wangdongxuking61/2015-Electronical-Competition-Code---Renesas-Cup/pictures/CAM00122.jpg

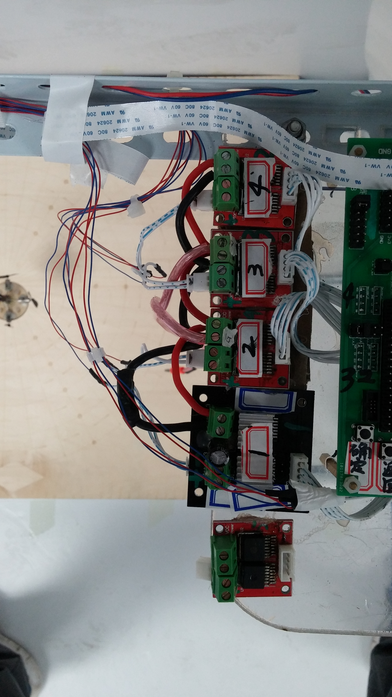
pictures/CAM00122.jpg
