wangdongxuking61/2015-Electronical-Competition-Code---Renesas-Cup/pictures/CAM00124.jpg

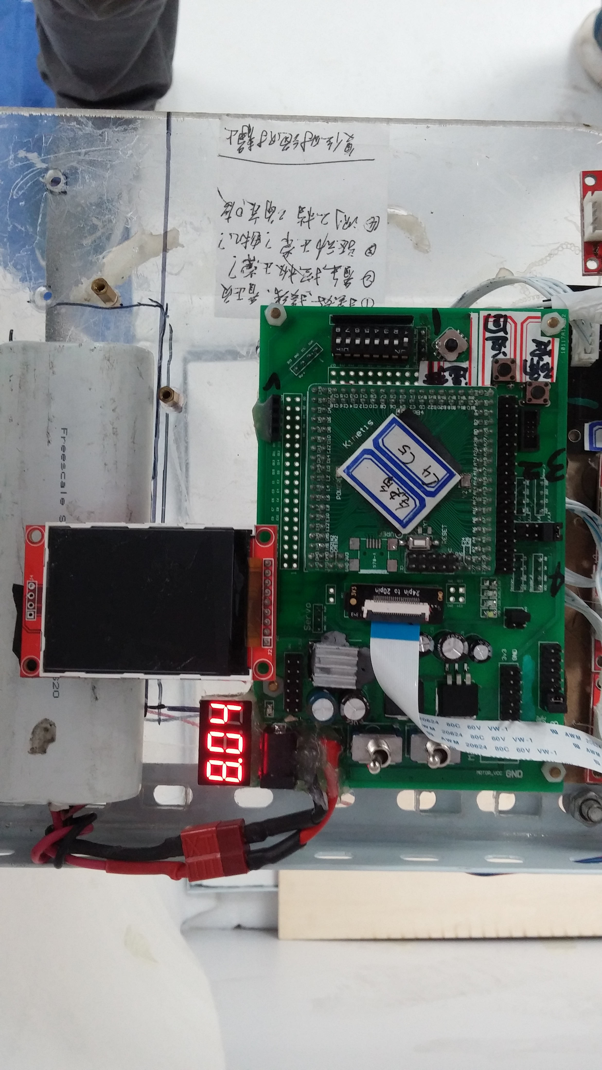
pictures/CAM00124.jpg
