wangdongxuking61/2015-Electronical-Competition-Code---Renesas-Cup/pictures/CAM00125.jpg

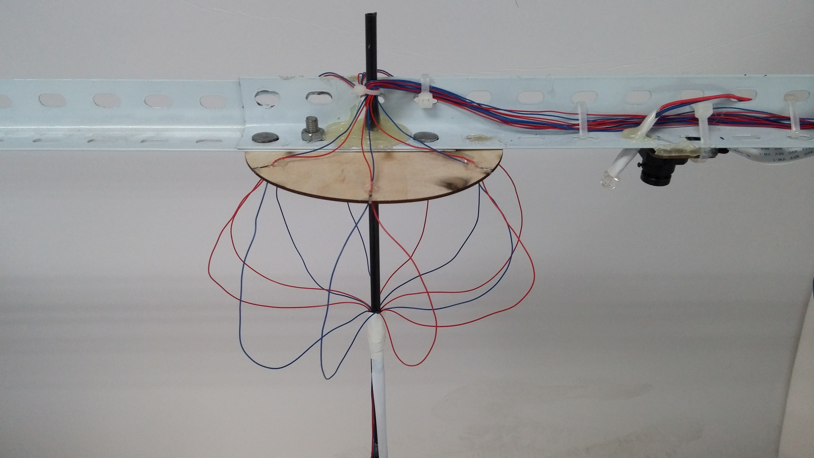
pictures/CAM00125.jpg
