wangdongxuking61/2015-Electronical-Competition-Code---Renesas-Cup/pictures/CAM00126.jpg

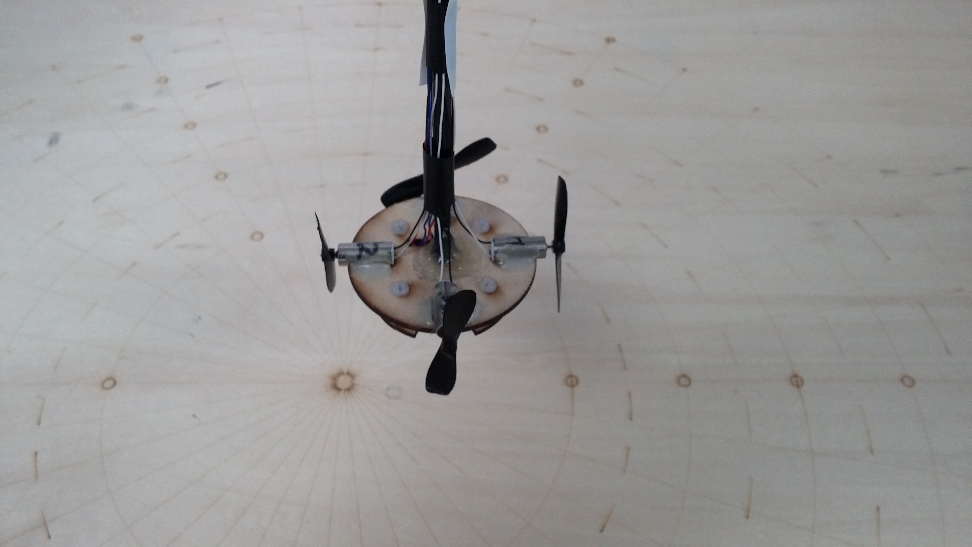
pictures/CAM00126.jpg
