wangdongxuking61/2015-Electronical-Competition-Code---Renesas-Cup/pictures/CAM00128.jpg

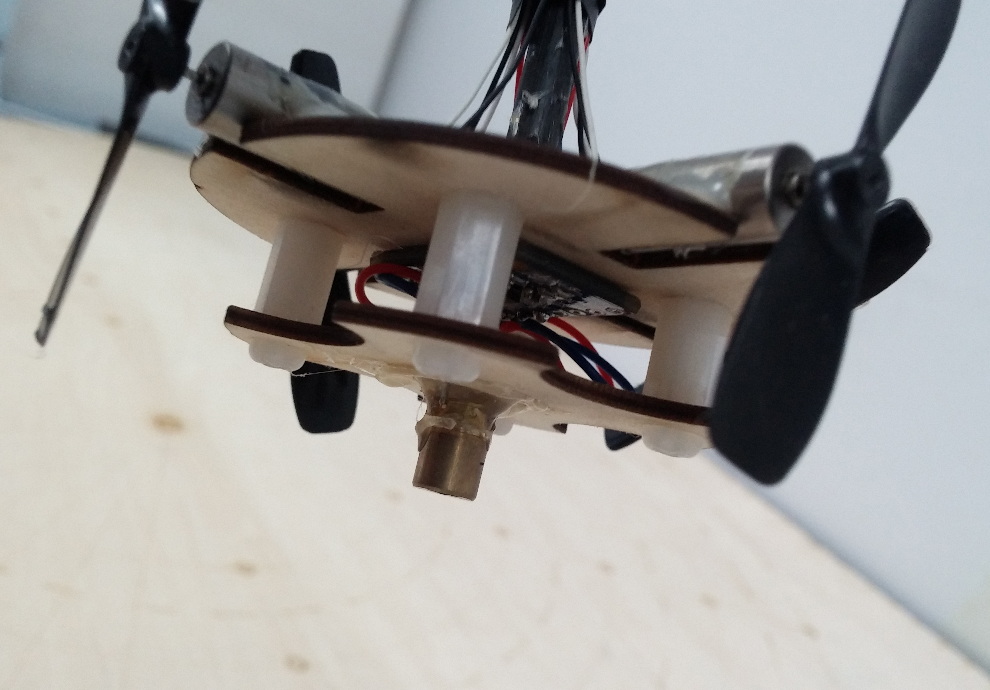
pictures/CAM00128.jpg
