wangdongxuking61/2015-Electronical-Competition-Code---Renesas-Cup/pictures/CAM00131.jpg

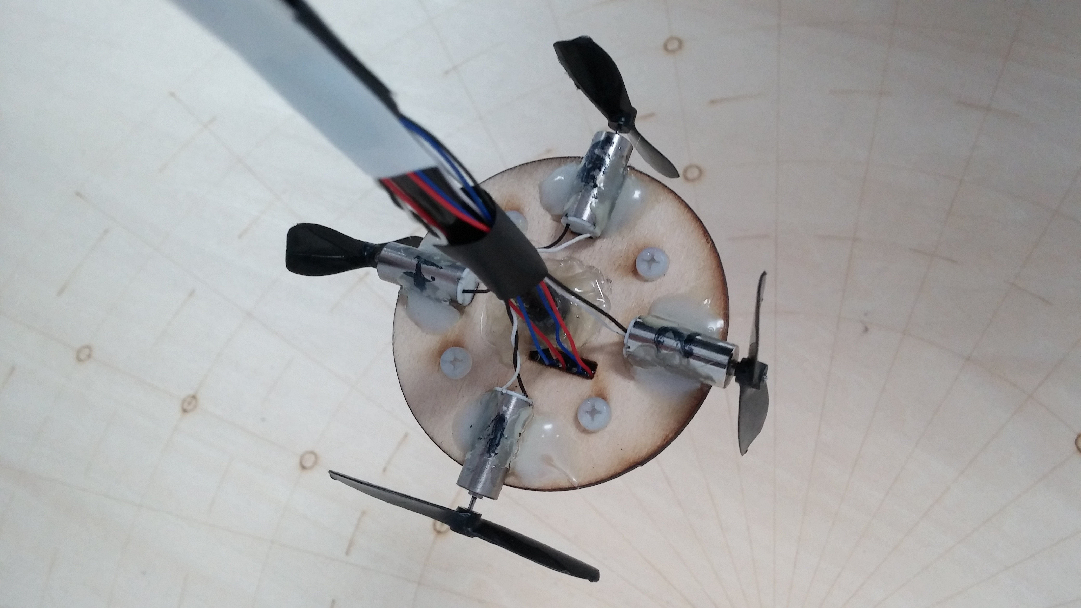
pictures/CAM00131.jpg
