wangdongxuking61/2015-Electronical-Competition-Code---Renesas-Cup/pictures/CAM00132.jpg

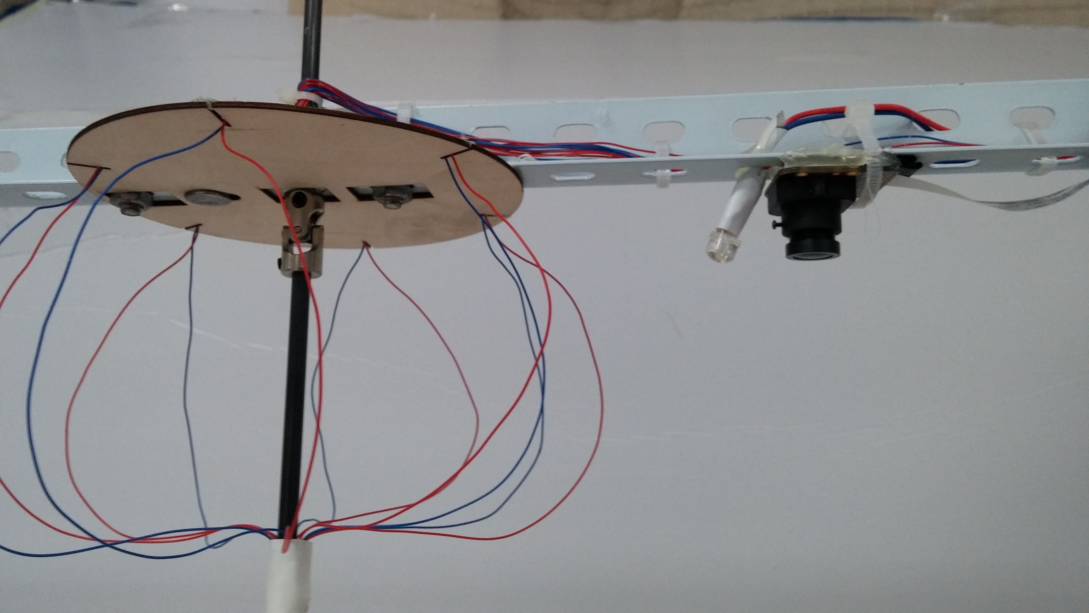
pictures/CAM00132.jpg
