wangdongxuking61/2015-Electronical-Competition-Code---Renesas-Cup/pictures/QQ截图20151103121053.png

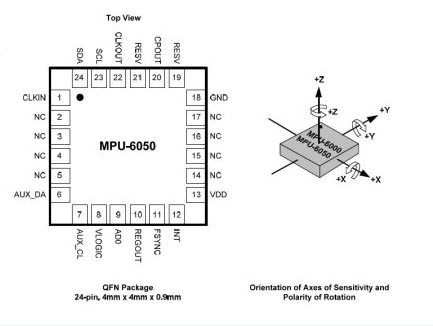
pictures/QQ截图20151103121053.png
