wangdongxuking61/2015-Electronical-Competition-Code---Renesas-Cup/pictures/TB1RlANHXXXXXb.XFXXXXXXXXXX_!!0-item_pic.jpg_400x400.jpg

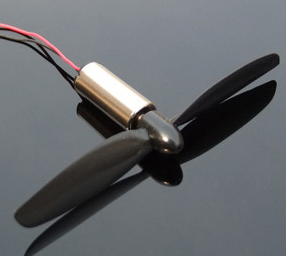
pictures/TB1RlANHXXXXXb.XFXXXXXXXXXX_!!0-item_pic.jpg_400x400.jpg
