wangdongxuking61/2015-Electronical-Competition-Code---Renesas-Cup/pictures/底座_下.png

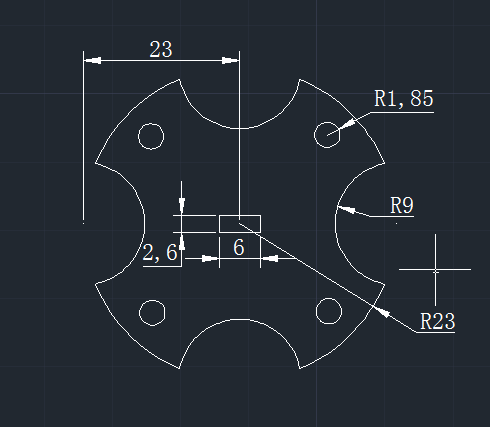
pictures/底座_下.png
