wangdongxuking61/2015-Electronical-Competition-Code---Renesas-Cup/pictures/电源.png

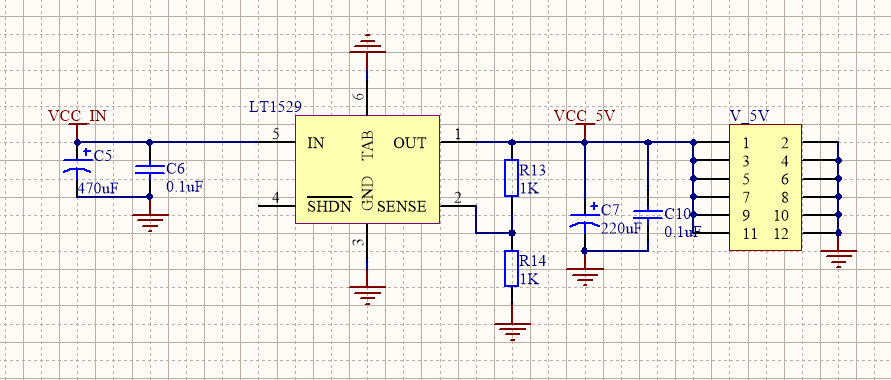
pictures/电源.png
