wangdongxuking61/2015-Electronical-Competition-Code---Renesas-Cup/pictures/硬件.png

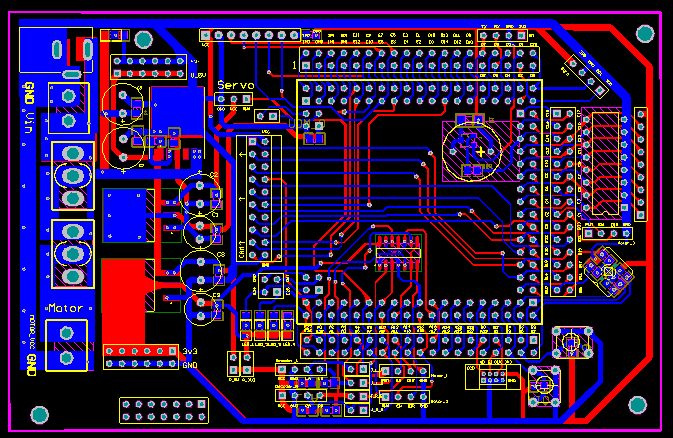
pictures/硬件.png
