wangdongxuking61/2015-Electronical-Competition-Code---Renesas-Cup/2015 Electronical Competition Code/src/app_mydriver/8x16.h

#ifndef _8x16_H
#define _8x16_H


/* XPM */
#define s ((((((((0
#define X )*2+1
#define _ )*2

unsigned char  Font8x16[] = {
/* pixels */

/* 0x00 */
s _ _ _ _ _ _ _ _ ,
s _ _ _ _ _ _ _ _ ,
s _ _ _ _ _ _ _ _ ,
s _ _ _ _ _ _ _ _ ,
s _ _ _ _ _ _ _ _ ,
s _ _ _ _ _ _ _ _ ,
s _ _ _ _ _ _ _ _ ,
s _ _ _ _ _ _ _ _ ,
s _ _ _ _ _ _ _ _ ,
s _ _ _ _ _ _ _ _ ,
s _ _ _ _ _ _ _ _ ,
s _ _ _ _ _ _ _ _ ,
s _ _ _ _ _ _ _ _ ,
s _ _ _ _ _ _ _ _ ,
s _ _ _ _ _ _ _ _ ,
s _ _ _ _ _ _ _ _ ,

/* 0x01 */
s _ _ _ _ _ _ _ _ ,
s _ _ _ _ _ _ _ _ ,
s _ _ _ _ _ _ _ _ ,
s _ _ _ _ _ _ _ _ ,
s _ _ _ _ _ _ _ _ ,
s _ _ _ _ _ _ _ _ ,
s _ _ _ _ _ _ _ _ ,
s _ _ _ _ _ _ _ _ ,
s _ _ _ _ _ _ _ _ ,
s _ _ _ _ _ _ _ _ ,
s _ _ _ _ _ _ _ _ ,
s _ _ _ _ _ _ _ _ ,
s _ _ _ _ _ _ _ _ ,
s _ _ _ _ _ _ _ _ ,
s _ _ _ _ _ _ _ _ ,
s _ _ _ _ _ _ _ _ ,

/* 0x02 */
s _ _ _ _ _ _ _ _ ,
s _ _ _ _ _ _ _ _ ,
s _ _ _ _ _ _ _ _ ,
s _ _ _ _ _ _ _ _ ,
s _ _ _ _ _ _ _ _ ,
s _ _ _ _ _ _ _ _ ,
s _ _ _ _ _ _ _ _ ,
s _ _ _ _ _ _ _ _ ,
s _ _ _ _ _ _ _ _ ,
s _ _ _ _ _ _ _ _ ,
s _ _ _ _ _ _ _ _ ,
s _ _ _ _ _ _ _ _ ,
s _ _ _ _ _ _ _ _ ,
s _ _ _ _ _ _ _ _ ,
s _ _ _ _ _ _ _ _ ,
s _ _ _ _ _ _ _ _ ,

/* 0x03 */
s _ _ _ _ _ _ _ _ ,
s _ _ _ _ _ _ _ _ ,
s _ _ _ _ _ _ _ _ ,
s _ _ _ _ _ _ _ _ ,
s _ _ _ _ _ _ _ _ ,
s _ _ _ _ _ _ _ _ ,
s _ _ _ _ _ _ _ _ ,
s _ _ _ _ _ _ _ _ ,
s _ _ _ _ _ _ _ _ ,
s _ _ _ _ _ _ _ _ ,
s _ _ _ _ _ _ _ _ ,
s _ _ _ _ _ _ _ _ ,
s _ _ _ _ _ _ _ _ ,
s _ _ _ _ _ _ _ _ ,
s _ _ _ _ _ _ _ _ ,
s _ _ _ _ _ _ _ _ ,

/* 0x04 */
s _ _ _ _ _ _ _ _ ,
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
s _ _ _ _ _ _ _ _ ,
s _ _ _ _ _ _ _ _ ,
s _ _ _ _ _ _ _ _ ,
s _ _ _ _ _ _ _ _ ,
s _ _ _ _ _ _ _ _ ,
s _ _ _ _ _ _ _ _ ,
s _ _ _ _ _ _ _ _ ,
s _ _ _ _ _ _ _ _ ,
s _ _ _ _ _ _ _ _ ,
s _ _ _ _ _ _ _ _ , 
s _ _ _ _ _ _ _ _ ,
s _ _ _ _ _ _ _ _ ,
};

#undef s
#undef X
#undef _

#endif
