wangdongxuking61/2015-Electronical-Competition-Code---Renesas-Cup/2015 Electronical Competition Code/src/app_mydriver/GB3232.H

#ifndef _GB3232_H
#define _GB3232_H


// ------------------  汉字字模的数据结构定义 ------------------------ //
struct  typFNT_GB32                 // 汉字字模数据结构 
{
       unsigned char  Index[3];               // 汉字内码索引	
       unsigned char   Msk[128];                        // 点阵码数据 
};

/////////////////////////////////////////////////////////////////////////
// 汉字字模表                                                          //
// 汉字库: 宋体32.dot,横向取模左高位,数据排列:从左到右从上到下         //
/////////////////////////////////////////////////////////////////////////
 struct  typFNT_GB32 codeGB_32[] =          // 数据表 
{

/*--  文字:  我  --*/
/*--  宋体22;  此字体下对应的点阵为：宽x高=32x32   --*/
"我",0x00,0x00,0x00,0x00,0x00,0x00,0x00,0x00,0x00,0x09,0xC0,0x00,0x00,0x7D,0xF8,0x00,
0x03,0xFD,0xCE,0x00,0x3F,0xC1,0xC7,0x00,0x00,0xC1,0xC7,0x00,0x00,0xC1,0xC3,0x00,
0x00,0xC1,0xC3,0x00,0x00,0xC1,0xC0,0xC0,0x3F,0xFF,0xFF,0xE0,0x20,0xC0,0xC0,0x00,
0x00,0xC0,0xC2,0x00,0x00,0xC0,0xC7,0x80,0x00,0xC2,0xC7,0x80,0x00,0xDE,0xCF,0x00,
0x00,0xF8,0xCE,0x00,0x0F,0xE0,0xFC,0x00,0x7F,0xC0,0xF8,0x00,0x3C,0xC0,0x78,0x00,
0x30,0xC0,0x70,0x20,0x00,0xC1,0xF8,0x20,0x00,0xC3,0xB8,0x20,0x00,0xC7,0x1E,0x20,
0x00,0xDC,0x0F,0x60,0x0F,0xF0,0x07,0xE0,0x03,0xC0,0x03,0xF0,0x01,0x80,0x00,0x70,
0x00,0x00,0x00,0x00,0x00,0x00,0x00,0x00,0x00,0x00,0x00,0x00,0x00,0x00,0x00,0x00,

/*--  文字:  爱  --*/
/*--  宋体22;  此字体下对应的点阵为：宽x高=32x32   --*/
"爱",0x00,0x00,0x00,0x00,0x00,0x00,0x03,0x00,0x00,0x00,0x3F,0x80,0x00,0x3F,0xFF,0x80,
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
0x00,0x40,0x00,0x00,0x00,0x00,0x00,0x00,0x00,0xE0,0x00,0x00,0x01,0xF0,0x00,0x00,
0x01,0xF0,0x00,0x00,0x01,0xF0,0x00,0x00,0x00,0xE0,0x00,0x00,0x00,0x00,0x00,0x00,
0x00,0x00,0x00,0x00,0x00,0x00,0x00,0x00,0x00,0x00,0x00,0x00,0x00,0x00,0x00,0x00,

 	

};	

#endif	
