wangdongxuking61/2015-Electronical-Competition-Code---Renesas-Cup/2015 Electronical Competition Code/src/app_mydriver/LCD.c

#include "include.h"
#include "char09.h"
#include "8X16.h"
#include "GB1616.h"	//16*16汉字字模
#include "GB3232.h"	//32*32汉字字模

/******************** (C) COPYRIGHT 2011 野火嵌入式开发工作室 ********************
 * 文件名       ：LCD.c
 * 描述         ：基于240*320LCD显示屏的底层驱动程序
 * 实验平台     ：凌立印象开发板
 * 库版本       ：基于野火库
 * 嵌入系统     ：
 * 作者         ：xuxu
**********************************************************************************/



/************************************************
*  函数名称：LCD_PORT_init
*  功能说明：240*320的SPI LCD引脚初始化
*  参数说明：无
*  函数返回：无0
*  修改时间：2014-1-14    已经测试
*************************************************/
void LCD_PORT_init()
{
    gpio_init(PORTE, 5, GPO, HIGH);//cs
    gpio_init(PORTE, 7, GPO, HIGH);//rst
    gpio_init(PORTE, 8, GPO, HIGH);//dc
    gpio_init(PORTE, 9, GPO, HIGH);//sdi
    gpio_init(PORTE,10, GPO, HIGH);//scl
}

/************************************************
*  函数名称：LCD_Reset
*  功能说明：240*320的SPI LCD复位
*  参数说明：无
*  函数返回：无
*  修改时间：2014-1-14    已经测试
*************************************************/
void LCD_Reset()
{
    reset = 0;
    delayms(20);
    reset = 1;
    delayms(20);
}


/************************************************
*  函数名称：LCD_Reset
*  功能说明：240*320的SPI LCD模块初始化
*  参数说明：direction取TRUE和FALSE，屏幕正反之分
*  函数返回：无
*  修改时间：2014-1-14    已经测试
*************************************************/
void LCD_init(unsigned char direction)
{
    //先端口输入输出配置
    LCD_PORT_init();
    
    reset=0;
    delayms(200);
    reset=1;
    delayms(200);
    //------------------------------------------------------------------//
    //-------------------Software Reset-------------------------------//
    write_command(0xCB);
    write_data(0x39);
    write_data(0x2C);
    write_data(0x00);
    write_data(0x34);
    write_data(0x02);

    write_command(0xCF);
    write_data(0x00);
    write_data(0XC1);
    write_data(0X30);

    write_command(0xE8);
    write_data(0x85);
    write_data(0x00);
    write_data(0x78);

    write_command(0xEA);
    write_data(0x00);
    write_data(0x00);

    write_command(0xED);
    write_data(0x64);
    write_data(0x03);
    write_data(0X12);
    write_data(0X81);

    write_command(0xF7);
    write_data(0x20);

    write_command(0xC0);    //Power control
    write_data(0x23);   //VRH[5:0]

    write_command(0xC1);    //Power control
    write_data(0x10);   //SAP[2:0];BT[3:0]

    write_command(0xC5);    //VCM control
    write_data(0x3e); //对比度调节
    write_data(0x28);

    write_command(0xC7);    //VCM control2
    write_data(0x86);  //--

    write_command(0x36);    // Memory Access Control
    if(direction)
        write_data(0xE8); //C8	   //48 68竖屏//28 E8 横屏
    else
        write_data(0x28);//0b00101000


    write_command(0x3A);
    write_data(0x55);

    write_command(0xB1);
    write_data(0x00);
    write_data(0x18);

    write_command(0xB6);    // Display Function Control
    write_data(0x08);
    write_data(0x82);
    write_data(0x27);

    write_command(0xF2);    // 3Gamma Function Disable
    write_data(0x00);

    write_command(0x26);    //Gamma curve selected
    write_data(0x01);

    write_command(0xE0);    //Set Gamma
    write_data(0x0F);
    write_data(0x31);
    write_data(0x2B);
    write_data(0x0C);
    write_data(0x0E);
    write_data(0x08);
    write_data(0x4E);
    write_data(0xF1);
    write_data(0x37);
    write_data(0x07);
    write_data(0x10);
    write_data(0x03);
    write_data(0x0E);
    write_data(0x09);
    write_data(0x00);

    write_command(0XE1);    //Set Gamma
    write_data(0x00);
    write_data(0x0E);
    write_data(0x14);
    write_data(0x03);
    write_data(0x11);
    write_data(0x07);
    write_data(0x31);
    write_data(0xC1);
    write_data(0x48);
    write_data(0x08);
    write_data(0x0F);
    write_data(0x0C);
    write_data(0x31);
    write_data(0x36);
    write_data(0x0F);

    write_command(0x11);    //Exit Sleep
    delayms(200);

    write_command(0x29);    //Display on
    write_command(0x2c);
}

/************************************************
*  函数名称：write_command
*  功能说明：LCD写指令函数
*  参数说明：c为指令
*  函数返回：无
*  修改时间：2014-1-14    已经测试
*************************************************/
void  write_command(unsigned char  c)
{
    cs=0;
    dcx=0;
    sdi=(GET_BITFIELD(c))->bit7;scl=0;scl=1;
    sdi=(GET_BITFIELD(c))->bit6;scl=0;scl=1;
    sdi=(GET_BITFIELD(c))->bit5;scl=0;scl=1;
    sdi=(GET_BITFIELD(c))->bit4;scl=0;scl=1;
    sdi=(GET_BITFIELD(c))->bit3;scl=0;scl=1;
    sdi=(GET_BITFIELD(c))->bit2;scl=0;scl=1;
    sdi=(GET_BITFIELD(c))->bit1;scl=0;scl=1;
    sdi=(GET_BITFIELD(c))->bit0;scl=0;scl=1;
    cs=1;
}

/************************************************
*  函数名称：write_data
*  功能说明：LCD写数据函数
*  参数说明：d为数据，为一个BYTE的数据
*  函数返回：无
*  修改时间：2014-1-14    已经测试
*************************************************/
void  write_data(unsigned char  d)
{
    cs=0;
    dcx=1;
    sdi=(GET_BITFIELD(d))->bit7;scl=0;scl=1;
    sdi=(GET_BITFIELD(d))->bit6;scl=0;scl=1;
    sdi=(GET_BITFIELD(d))->bit5;scl=0;scl=1;
    sdi=(GET_BITFIELD(d))->bit4;scl=0;scl=1;
    sdi=(GET_BITFIELD(d))->bit3;scl=0;scl=1;
    sdi=(GET_BITFIELD(d))->bit2;scl=0;scl=1;
    sdi=(GET_BITFIELD(d))->bit1;scl=0;scl=1;
    sdi=(GET_BITFIELD(d))->bit0;scl=0;scl=1;
    cs=1;
}

/************************************************
*  函数名称：write_word
*  功能说明：LCD写数据函数
*  参数说明：dat为数据，为两个BYTE的数据
*  函数返回：无
*  修改时间：2014-1-14    已经测试
*************************************************/
void write_word(unsigned int dat)
{
    write_data(dat>>8);
    write_data(dat);
}






/************************************************
*  函数名称：RamAdressSet
*  功能说明：LCD的设置RAM地址
*  参数说明：无
*  函数返回：无
*  修改时间：2014-1-14    已经测试
*************************************************/
void  RamAdressSet()
{
    write_command(0x2A);
    write_data(0x00);
    write_data(0x00);
    write_data(0x00);
    write_data(0xaf);

    write_command(0x2B);
    write_data(0x00);
    write_data(0x00);
    write_data(0x00);
    write_data(0xdb);		
}


/************************************************
*  函数名称：LCD_SetPos
*  功能说明：LCD的设置写入屏幕的地址
*  参数说明：横坐标X0~X1，纵坐标为Y0~Y1
*  函数返回：无
*  修改时间：2014-1-14    已经测试
*************************************************/
void LCD_SetPos(unsigned int x0,unsigned int x1,unsigned int y0,unsigned int y1)
{
    write_command(0x2A);
    write_data(x0>>8);
    write_data(x0);
    write_data(x1>>8);
    write_data(x1);

    write_command(0x2B);
    write_data(y0>>8);
    write_data(y0);
    write_data(y1>>8);
    write_data(y1);
    write_command(0x2c);
}

/************************************************
*  函数名称：LCD_PutChar
*  功能说明：LCD的写一个Char，默认为8*16的字模
*  参数说明：横坐标x，纵坐标为y，c为数据，fColor为字颜色，bColor为背景颜色
*  函数返回：无
*  修改时间：2014-1-14    已经测试
*************************************************/
void LCD_PutChar(unsigned int x, unsigned int y,unsigned char c, unsigned int fColor, unsigned int bColor)
{
    LCD_PutChar8x16( x, y, c, fColor, bColor );
}


/************************************************
*  函数名称：LCD_PutString
*  功能说明：LCD的写字符串
*  参数说明：横坐标x，纵坐标为y，s为字符串指针，fColor为字颜色，bColor为背景颜色
*  函数返回：无
*  修改时间：2014-1-14    已经测试
*************************************************/
void LCD_PutString(unsigned int x, unsigned int y, unsigned char *s, unsigned int fColor, unsigned int bColor)
{
    unsigned char l=0;
    while(*s) {
        if( *s < 0x80)
        {
            LCD_PutChar(x+l*8,y,*s,fColor,bColor);
            s++;l++;
        }
        else
        {
            PutGB1616(x+l*8,y,(unsigned char*)s,fColor,bColor);
            s+=2;l+=2;
        }
    }
}


/************************************************
*  函数名称：LCD_PutChar8x16
*  功能说明：LCD的写字符串8*16字模
*  参数说明：横坐标x，纵坐标为y，c为ASCII码，fColor为字颜色，bColor为背景颜色
*  函数返回：无
*  修改时间：2014-1-14    已经测试
*************************************************/
void LCD_PutChar8x16(unsigned int x, unsigned int y,unsigned char c, unsigned int fColor, unsigned int bColor)
{
    unsigned int i,j;
    LCD_SetPos(x,x+8-1,y,y+16-1);
    for(i=0; i<16;i++)
    {
	unsigned char m=Font8x16[c*16+i];
	for(j=0;j<8;j++)
	{
            if((m&0x80)==0x80)
                write_word(fColor);
            else
                write_word(bColor);
            m<<=1;
	}
    }
}

/************************************************
*  函数名称：PutGB1616
*  功能说明：LCD的写汉字16*16字模
*  参数说明：横坐标x，纵坐标为y，c[2]为汉子的机内码，fColor为字颜色，bColor为背景颜色
*  函数返回：无
*  修改时间：2014-1-14    已经测试
*  备注    ：需要自建汉子库codeGB_16
*************************************************/
void PutGB1616(unsigned int x, unsigned int  y, unsigned char c[2], unsigned int fColor,unsigned int bColor)
{
    unsigned int i,j,k;
    LCD_SetPos(x,  x+16-1,y, y+16-1);
    for (k=0;k<64;k++)
    { //64标示自建汉字库中的个数，循环查询内码
        if ((codeGB_16[k].Index[0]==c[0])&&(codeGB_16[k].Index[1]==c[1]))
        {
            for(i=0;i<32;i++)
            {
                unsigned short m=codeGB_16[k].Msk[i];
                for(j=0;j<8;j++)
                {
                    if((m&0x80)==0x80)
                        write_word(fColor);
                    else
                        write_word(bColor);
                    m<<=1;
                }
            }
        }
    }
}

/************************************************
*  函数名称：PutGB3232
*  功能说明：LCD的写汉字32*32字模
*  参数说明：横坐标x，纵坐标为y，c[2]为汉子的机内码，fColor为字颜色，bColor为背景颜色
*  函数返回：无
*  修改时间：2014-1-14    已经测试
*  备注    ：需要自建汉子库codeGB_32
*************************************************/
void PutGB3232(unsigned int x, unsigned int  y, unsigned char c[2], unsigned int fColor,unsigned int bColor)
{
    unsigned int i,j,k;
    LCD_SetPos(x,  x+32-1,y, y+32-1);
    for (k=0;k<15;k++) { //15标示自建汉字库中的个数，循环查询内码
        if ((codeGB_32[k].Index[0]==c[0])&&(codeGB_32[k].Index[1]==c[1])){
            for(i=0;i<128;i++) {
                unsigned short m=codeGB_32[k].Msk[i];
                for(j=0;j<8;j++) {
                    if((m&0x80)==0x80) {
                        write_word(fColor);
                    }
                    else {
                        write_word(bColor);
                    }
                    m<<=1;
                }
            }
        }
    }	
}


/************************************************
*  函数名称：Disp_single_colour
*  功能说明：LCD的刷屏函数
*  参数说明：Color为背景颜色
*  函数返回：无
*  修改时间：2014-1-14    已经测试
*************************************************/
void Disp_single_colour(unsigned int color)
{
    unsigned int i,j;
    LCD_SetPos(0,320-1,0,240-1);
    for (i=0;i<240;i++)
        for (j=0;j<320;j++)
            write_word(color);
}


/************************************************
*  函数名称：Draw_single_line
*  功能说明：LCD的画单线函数
*  参数说明：axis为行或者列，取'H'或者'L'，line为第几行或者第几列，Color为颜色
*  函数返回：无
*  修改时间：2014-1-14    已经测试
*************************************************/
void Draw_single_line(unsigned char axis,unsigned int line,unsigned int color)
{
    unsigned int i;
    if(axis=='L')
    {
        LCD_SetPos(line,line,0,240-1);
        for (i=0;i<240;i++)
            write_word(color);
    }
    else if(axis=='H')
    {
        LCD_SetPos(0,320-1,line,line);
        for (i=0;i<320;i++)
            write_word(color);
    }
}



/************************************************
*  函数名称：LCD_Put_Unsigned_Int
*  功能说明：LCD的显示Unsigned_Int
*  参数说明：x，y为坐标，s0为要先写的字符串，pnum为数值，fColor和bColor为字和底色
*  函数返回：无
*  修改时间：2014-1-14    已经测试
*************************************************/
void LCD_Put_Unsigned_Int(unsigned int x,unsigned int y,unsigned char s0[],unsigned int pnum,unsigned int fColor, unsigned int bColor)
{
    unsigned char l=0;
    unsigned char s[30];
    unsigned char count=0;
    //copy
    count=0;
    while(s0[count])
    {
       s[count] = s0[count];
       count++;
    }
    //strcat
    if(pnum<10)
    {  s[count]=pnum+'0';s[count+1]='\0';}
    else if((10<=pnum)&&(pnum<100))
    {  s[count]=pnum/10+'0';s[count+1]=pnum%10+'0';s[count+2]='\0';}
    else if(pnum<=999)
    {
        s[count]=pnum/100+'0';
        s[count+1]=pnum/10%10+'0';
        s[count+2]=pnum%10+'0';
        s[count+3]='\0';
    }
    else if(pnum<=9999)
    {
        s[count]=pnum/1000+'0';
        s[count+1]=pnum/100%10+'0';
        s[count+2]=pnum/10%10+'0';
        s[count+3]=pnum%10+'0';
        s[count+4]='\0';
    }
    else if(pnum<=99999)
    {
        s[count]=pnum/10000+'0';
        s[count+1]=pnum/1000%10+'0';
        s[count+2]=pnum/100%10+'0';
        s[count+3]=pnum/10%10+'0';
        s[count+4]=pnum%10+'0';
        s[count+5]='\0';
    }
    count=0;
    while(s[count])
    {
        if( s[count] < 0x80)
        {
            LCD_PutChar(x+l*8,y,s[count],fColor,bColor);
            count++;
            l++;
        }
        else
        {
            PutGB1616(x+l*8,y,(unsigned char*)s[count],fColor,bColor);
            count+=2;
            l+=2;
        }
    }
}


/************************************************
*  函数名称：LCD_Put_Int
*  功能说明：LCD的显示Unsigned_Int
*  参数说明：x，y为坐标，s0为要先写的字符串，pnum为数值，fColor和bColor为字和底色
*  函数返回：无
*  修改时间：2014-1-14    已经测试
*************************************************/
void LCD_Put_Int(unsigned int x,unsigned int y,unsigned char s0[],int pnum,unsigned int fColor, unsigned int bColor)
{
    unsigned char l=0;
    unsigned char s[30];
    unsigned char count=0;
    //copy
    count=0;
    while(s0[count])
    {
       s[count] = s0[count];
       count++;
    }
    //strcat
    if(pnum < 0)
    {
       s[count] = '-';
       count++;
       pnum = (-1) * pnum;
    }
    if(pnum < 10)
    {  s[count]=pnum+'0';s[count+1]='\0';}
    else if((10<=pnum)&&(pnum<100))
    {  s[count]=pnum/10+'0';s[count+1]=pnum%10+'0';s[count+2]='\0';}
    else if(pnum<=999)
    {
        s[count]=pnum/100+'0';
        s[count+1]=pnum/10%10+'0';
        s[count+2]=pnum%10+'0';
        s[count+3]='\0';
    }
    else if(pnum<=9999)
    {
        s[count]=pnum/1000+'0';
        s[count+1]=pnum/100%10+'0';
        s[count+2]=pnum/10%10+'0';
        s[count+3]=pnum%10+'0';
        s[count+4]='\0';
    }
    else if(pnum<=99999)
    {
        s[count]=pnum/10000+'0';
        s[count+1]=pnum/1000%10+'0';
        s[count+2]=pnum/100%10+'0';
        s[count+3]=pnum/10%10+'0';
        s[count+4]=pnum%10+'0';
        s[count+5]='\0';
    }
    count=0;
    while(s[count])
    {
        if( s[count] < 0x80)
        {
            LCD_PutChar(x+l*8,y,s[count],fColor,bColor);
            count++;
            l++;
        }
        else
        {
            PutGB1616(x+l*8,y,(unsigned char*)s[count],fColor,bColor);
            count+=2;
            l+=2;
        }
    }
}


/************************************************
*  函数名称：LCD_Put_Int
*  功能说明：LCD的显示Unsigned_Int
*  参数说明：x，y为坐标，s0为要先写的字符串，f为数值，fColor和bColor为字和底色
*  函数返回：无
*  修改时间：2014-1-14    已经测试
*************************************************/
void LCD_Put_Float(unsigned int x,unsigned int y,unsigned char s0[],float f,unsigned int fColor, unsigned int bColor)
{
    unsigned char l=0;
    unsigned char s[30];
    unsigned char count=0;
    int pnum;
    //copy
    count=0;
    while(s0[count])
    {
       s[count] = s0[count];
       count++;
    }
    //strcat
    pnum = (int)(f);
    if(pnum < 0)
    {
       s[count++] = '-';
       pnum = (-1) * pnum;
    }
    if(pnum < 10)
    {
        s[count++]=pnum+'0';
    }
    else if((10<=pnum)&&(pnum<100))
    {
        s[count++]=pnum/10+'0';
        s[count++]=pnum%10+'0';
    }
    else if(pnum<=999)
    {
        s[count++]=pnum/100+'0';
        s[count++]=pnum/10%10+'0';
        s[count++]=pnum%10+'0';
    }
    else if(pnum<=9999)
    {
        s[count++]=pnum/1000+'0';
        s[count++]=pnum/100%10+'0';
        s[count++]=pnum/10%10+'0';
        s[count++]=pnum%10+'0';
    }
    else if(pnum<=99999)
    {
        s[count++]=pnum/10000+'0';
        s[count++]=pnum/1000%10+'0';
        s[count++]=pnum/100%10+'0';
        s[count++]=pnum/10%10+'0';
        s[count++]=pnum%10+'0';
    }
    //小数点后面三位
    if(f<0)
        f=(-1)*f;
    s[count++] = '.';
    s[count++] = ((int)(f*10))%10 + '0';
    s[count++] = ((int)(f*100))%10 + '0';
    s[count++] = ((int)(f*1000))%10 + '0';

    //print
    count=0;
    while(s[count])
    {
        if( s[count] < 0x80)
        {
            LCD_PutChar(x+l*8,y,s[count],fColor,bColor);
            count++;
            l++;
        }
        else
        {
            PutGB1616(x+l*8,y,(unsigned char*)s[count],fColor,bColor);
            count+=2;
            l+=2;
        }
    }
}

/************************************************
*  函数名称：Print_child
*  功能说明：LCD的显示一个小破孩图片
*  参数说明：无
*  函数返回：无
*  修改时间：2014-1-14    已经测试
*************************************************/
void Print_child()
{
    unsigned char child[]={255,255,255,255,255,255,255,255,255,255,255,255,255,255,255,255,255,255,255,255,255,255,255,255,255,255,255,255,255,255,255,255,255,255,255,255,255,255,255,255,255,255,255,255,255,255,255,255,255,255,255,255,255,255,255,255,255,255,255,255,255,255,255,255,255,255,255,255,255,255,255,255,255,255,255,255,255,255,255,255,255,255,255,255,255,255,255,255,255,255,255,255,255,255,255,255,255,255,255,255,255,255,255,255,255,255,255,255,255,255,255,255,255,255,255,255,255,255,255,255,255,255,255,255,255,255,255,255,255,255,255,255,255,255,255,255,255,255,255,255,255,255,255,255,255,255,255,255,255,255,255,255,255,255,255,255,255,255,255,255,255,255,255,255,255,255,255,255,255,255,255,255,255,255,255,255,255,255,255,255,255,255,255,255,255,255,255,255,255,255,255,255,255,255,255,255,255,255,255,255,255,255,255,255,255,255,255,255,255,255,255,255,255,255,255,255,255,255,255,255,255,255,255,255,255,255,255,255,255,255,255,255,255,255,255,255,255,255,255,255,255,255,255,255,255,255,255,255,255,255,255,255,255,255,255,255,255,255,255,255,255,255,255,255,255,255,255,255,255,255,255,255,255,255,255,255,255,255,255,255,255,255,255,255,255,255,255,255,255,255,255,255,255,255,255,255,255,255,255,255,255,255,255,255,255,255,255,255,255,255,255,255,255,255,255,255,255,255,255,255,255,255,255,255,255,255,255,255,255,255,255,255,255,255,255,255,255,255,255,255,255,255,255,255,255,255,255,255,255,255,255,255,255,255,255,255,255,255,255,255,255,255,255,255,255,255,255,255,2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
255,255,255,255,255,255,255,255,255,255,255,255,255,255,255,255,255,255,255,255,255,255,255,255,255,255,255,255,255,255,255,255,255,255,255,255,255,255,255,255,255,255,255,255,255,255,255,255,255,255,255,255,255,255,255,255,255,255,255,255,255,255,255,255,255,255,255,255};
    unsigned int i=0;
    LCD_SetPos(0,256-1,0,200-1);
    for (i=0;i<6400;i++)
    {
        if((GET_BITFIELD(child[i]))->bit7)write_word(White);else write_word(Black);
        if((GET_BITFIELD(child[i]))->bit6)write_word(White);else write_word(Black);
        if((GET_BITFIELD(child[i]))->bit5)write_word(White);else write_word(Black);
        if((GET_BITFIELD(child[i]))->bit4)write_word(White);else write_word(Black);
        if((GET_BITFIELD(child[i]))->bit3)write_word(White);else write_word(Black);
        if((GET_BITFIELD(child[i]))->bit2)write_word(White);else write_word(Black);
        if((GET_BITFIELD(child[i]))->bit1)write_word(White);else write_word(Black);
        if((GET_BITFIELD(child[i]))->bit0)write_word(White);else write_word(Black);
    }
}



/*************************************************************************
*  函数名称：Send_Image_to_LCD
*  功能说明：在显示屏上显示鹰眼图像
*  参数说明：img为指针
*  函数返回：无
*  修改时间：2012-2-14    已测试
*************************************************************************/
void Send_Image_to_LCD(unsigned char img[CAMERA_H][CAMERA_DMA_NUM])
{
    int i,j,k;
    LCD_SetPos(0,320-1,0,CAMERA_H-1);
    for(i=0;i < CAMERA_H - 20;i++)
    {
        for(j = 0;j < CAMERA_DMA_NUM; j++)
            for(k = 0;k < 8; k++)
                if(img[i][j]&(0x80>>k))              
                    write_word(Black);	//写图像数据
                else
                    write_word(White);		//写图像数据     
    }
}


/*************************************************************************
*  函数名称：LcdPrintAnglePara
*  功能说明：在显示屏上显示鹰眼图像
*  参数说明：img为指针
*  函数返回：无
*  修改时间：2012-2-14    已测试
*************************************************************************/
void LcdPrintAnglePara()
{
    int i = 0;
    char str[40];
    
    sprintf(str,"Acc_Off:%d,%d,%d",Acc_Offset.y,Acc_Offset.z);//,%.0f,%.0f
    LCD_PutString(20,i,str,Red,Green);   i+=20;
    return;
    sprintf(str,"Acc_ADC :%.0f,%.0f,%.0f",Acc_ADC.x,Acc_ADC.y,Acc_ADC.z);
    LCD_PutString(20,i,str,Red,Green);   i+=20;
    sprintf(str,"Acc_Data:%.0f,%.0f,%.0f",Acc_ADC_Data.x,Acc_ADC_Data.y,Acc_ADC_Data.z);
    LCD_PutString(20,i,str,Red,Green);   i+=20;
    sprintf(str,"");
    LCD_PutString(20,i,str,Red,Green);   i+=20;
    
    
    sprintf(str,"Gyro_Offt:%.0f,%.0f,%.0f",Gyro_Offset.x,Gyro_Offset.y,Gyro_Offset.z);
    LCD_PutString(20,i,str,Red,Green);   i+=20;
    sprintf(str,"Gyro_ADC :%.0f,%.0f,%.0f",Gyro_ADC.x,Gyro_ADC.y,Gyro_ADC.z);
    LCD_PutString(20,i,str,Red,Green);   i+=20;
    sprintf(str,"Gyro_dps :%.2f,%.2f,%.2f",Gyro_dps.x,Gyro_dps.y,Gyro_dps.z);
    LCD_PutString(20,i,str,Red,Green);   i+=20;
    sprintf(str,"");
    LCD_PutString(20,i,str,Red,Green);   i+=20;
    
    sprintf(str,"Angle:%.2f,%.2f,%.2f",Angle.roll,Angle.pitch,Angle.yaw);
    LCD_PutString(20,i,str,Red,Green);   i+=20;
    sprintf(str,"");
    LCD_PutString(20,i,str,Red,Green);   i+=20;
   
    sprintf(str,"Q:%.3f,%.3f,%.3f,%.3f",Q.q1,Q.q2,Q.q3,Q.q4);
    LCD_PutString(20,i,str,Red,Green);   i+=20;
    sprintf(str,"");
    LCD_PutString(20,i,str,Red,Green);   i+=20;
}


/*显示大的数字*/
void printBigNum(int time1s,int sety)
{
    static int recordPer[2]={0,1};
    //十位
    if(recordPer[0]!=time1s/10)
    {
        recordPer[0]=time1s/10;
        LCD_SetPos(20,20+Width-1,sety,sety+Height-1);
        printNum(recordPer[0]);
    }
    //个位
    if(recordPer[1]!=time1s%10)
    {
        recordPer[1]=time1s%10;
        LCD_SetPos(20+Width,20+2*Width-1,sety,sety+Height-1);
        printNum(recordPer[1]);
    }
}


/*显示大的数字*/
void printNum(int n)
{
    for (int y=0;y<WidthNum*Height;y++)
    {
        for (int k=0;k<8;k++)
            if(num[n][y]&(0x80>>k))
                write_word(Red);
            else 
                write_word(Green);
    }
}



/*************************************************************************
*  函数名称：Process_Image
*  功能说明：处理图像信息，算出中线值，并且算出偏差来量
*  参数说明：无
*  函数返回：无
*  修改时间：2012-2-14    已测试
*  运行时间：?ms,在200M情况下
*************************************************************************/
void Process_Image()
{
    static unsigned char ImageData[320];
    
    int sumH=0,sumL=0;
    int cnt=0;
    
	//就是做了个x轴和y轴的黑点的坐标平均数，简单吧。。。但是黑色碳素杆要贴白色胶带，宁白勿黑
    for(int hang=10;hang<140;hang++)
    {
        //解压
        for(int i=0;i<40;i++)
            for(int k=0;k<8;k++)
                ImageData[i*8+k] = (Image_fire[hang][i]>>(7-k))&0x01;
        //处理
        for(int j=70;j<200;j++)
            if(ImageData[j]==1)
            {
                sumH += hang;
                sumL += j;
                cnt++;
            }
    }
    
    Angle.aveH = (int)(sumH /(float)cnt);
    Angle.aveL = (int)(sumL /(float)cnt);  
    Angle.startImage = 1;
}
