wangdongxuking61/2015-Electronical-Competition-Code---Renesas-Cup/2015 Electronical Competition Code/src/drivers/gpio/gpio_cfg.h

/******************** (C) COPYRIGHT 2011 野火嵌入式开发工作室 ********************
 * 文件名       ：gpio_cfg.h
 * 描述         ：gpio的端口定义头文件
 *
 * 实验平台     ：野火kinetis开发板
 * 库版本       ：
 * 嵌入系统     ：
 *
 * 作者         ：野火嵌入式开发工作室
 * 淘宝店       ：http://firestm32.taobao.com
 * 技术支持论坛 ：http://www.ourdev.cn/bbs/bbs_list.jsp?bbs_id=1008
**********************************************************************************/
#ifndef __GPIO_CFG_H__
#define __GPIO_CFG_H__




//定义PTA的端口  ——by 野火
#define PTA0_OUT     PTA_BASE_PTR->PDORs.PDOR0
#define PTA1_OUT     PTA_BASE_PTR->PDORs.PDOR1
#define PTA2_OUT     PTA_BASE_PTR->PDORs.PDOR2
#define PTA3_OUT     PTA_BASE_PTR->PDORs.PDOR3
#define PTA4_OUT     PTA_BASE_PTR->PDORs.PDOR4
#define PTA5_OUT     PTA_BASE_PTR->PDORs.PDOR5
#define PTA6_OUT     PTA_BASE_PTR->PDORs.PDOR6
#define PTA7_OUT     PTA_BASE_PTR->PDORs.PDOR7
#define PTA8_OUT     PTA_BASE_PTR->PDORs.PDOR8
#define PTA9_OUT     PTA_BASE_PTR->PDORs.PDOR9
#define PTA10_OUT    PTA_BASE_PTR->PDORs.PDOR10
#define PTA11_OUT    PTA_BASE_PTR->PDORs.PDOR11
#define PTA12_OUT    PTA_BASE_PTR->PDORs.PDOR12
#define PTA13_OUT    PTA_BASE_PTR->PDORs.PDOR13
#define PTA14_OUT    PTA_BASE_PTR->PDORs.PDOR14
#define PTA15_OUT    PTA_BASE_PTR->PDORs.PDOR15
#define PTA16_OUT    PTA_BASE_PTR->PDORs.PDOR16
#define PTA17_OUT    PTA_BASE_PTR->PDORs.PDOR17
#define PTA18_OUT    PTA_BASE_PTR->PDORs.PDOR18
#define PTA19_OUT    PTA_BASE_PTR->PDORs.PDOR19
#define PTA20_OUT    PTA_BASE_PTR->PDORs.PDOR20
#define PTA21_OUT    PTA_BASE_PTR->PDORs.PDOR21
#define PTA22_OUT    PTA_BASE_PTR->PDORs.PDOR22
#define PTA23_OUT    PTA_BASE_PTR->PDORs.PDOR23
#define PTA24_OUT    PTA_BASE_PTR->PDORs.PDOR24
#define PTA25_OUT    PTA_BASE_PTR->PDORs.PDOR25
#define PTA26_OUT    PTA_BASE_PTR->PDORs.PDOR26
#define PTA27_OUT    PTA_BASE_PTR->PDORs.PDOR27
#define PTA28_OUT    PTA_BASE_PTR->PDORs.PDOR28
#define PTA29_OUT    PTA_BASE_PTR->PDORs.PDOR29
#define PTA30_OUT    PTA_BASE_PTR->PDORs.PDOR30
#define PTA31_OUT    PTA_BASE_PTR->PDORs.PDOR31

//定义PTB的端口  ——by 野火
#define PTB0_OUT     PTB_BASE_PTR->PDORs.PDOR0
#define PTB1_OUT     PTB_BASE_PTR->PDORs.PDOR1
#define PTB2_OUT     PTB_BASE_PTR->PDORs.PDOR2
#define PTB3_OUT     PTB_BASE_PTR->PDORs.PDOR3
#define PTB4_OUT     PTB_BASE_PTR->PDORs.PDOR4
#define PTB5_OUT     PTB_BASE_PTR->PDORs.PDOR5
#define PTB6_OUT     PTB_BASE_PTR->PDORs.PDOR6
#define PTB7_OUT     PTB_BASE_PTR->PDORs.PDOR7
#define PTB8_OUT     PTB_BASE_PTR->PDORs.PDOR8
#define PTB9_OUT     PTB_BASE_PTR->PDORs.PDOR9
#define PTB10_OUT    PTB_BASE_PTR->PDORs.PDOR10
#define PTB11_OUT    PTB_BASE_PTR->PDORs.PDOR11
#define PTB12_OUT    PTB_BASE_PTR->PDORs.PDOR12
#define PTB13_OUT    PTB_BASE_PTR->PDORs.PDOR13
#define PTB14_OUT    PTB_BASE_PTR->PDORs.PDOR14
#define PTB15_OUT    PTB_BASE_PTR->PDORs.PDOR15
#define PTB16_OUT    PTB_BASE_PTR->PDORs.PDOR16
#define PTB17_OUT    PTB_BASE_PTR->PDORs.PDOR17
#define PTB18_OUT    PTB_BASE_PTR->PDORs.PDOR18
#define PTB19_OUT    PTB_BASE_PTR->PDORs.PDOR19
#define PTB20_OUT    PTB_BASE_PTR->PDORs.PDOR20
#define PTB21_OUT    PTB_BASE_PTR->PDORs.PDOR21
#define PTB22_OUT    PTB_BASE_PTR->PDORs.PDOR22
#define PTB23_OUT    PTB_BASE_PTR->PDORs.PDOR23
#define PTB24_OUT    PTB_BASE_PTR->PDORs.PDOR24
#define PTB25_OUT    PTB_BASE_PTR->PDORs.PDOR25
#define PTB26_OUT    PTB_BASE_PTR->PDORs.PDOR26
#define PTB27_OUT    PTB_BASE_PTR->PDORs.PDOR27
#define PTB28_OUT    PTB_BASE_PTR->PDORs.PDOR28
#define PTB29_OUT    PTB_BASE_PTR->PDORs.PDOR29
#define PTB30_OUT    PTB_BASE_PTR->PDORs.PDOR30
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
#define PTE_BYTE3_OUT   PTE_BASE_PTR->PDORByte.Byte3


//定义PTA的8位输出输入方向  ——by 野火
#define DDRA_BYTE0   PTA_BASE_PTR->DDRByte.Byte0
#define DDRA_BYTE1   PTA_BASE_PTR->DDRByte.Byte1
#define DDRA_BYTE2   PTA_BASE_PTR->DDRByte.Byte2
#define DDRA_BYTE3   PTA_BASE_PTR->DDRByte.Byte3

//定义PTB的8位输出输入方向  ——by 野火
#define DDRB_BYTE0   PTB_BASE_PTR->DDRByte.Byte0
#define DDRB_BYTE1   PTB_BASE_PTR->DDRByte.Byte1
#define DDRB_BYTE2   PTB_BASE_PTR->DDRByte.Byte2
#define DDRB_BYTE3   PTB_BASE_PTR->DDRByte.Byte3

//定义PTC的8位输出输入方向  ——by 野火
#define DDRC_BYTE0   PTC_BASE_PTR->DDRByte.Byte0
#define DDRC_BYTE1   PTC_BASE_PTR->DDRByte.Byte1
#define DDRC_BYTE2   PTC_BASE_PTR->DDRByte.Byte2
#define DDRC_BYTE3   PTC_BASE_PTR->DDRByte.Byte3

//定义PTD的8位输出输入方向  ——by 野火
#define DDRD_BYTE0   PTD_BASE_PTR->DDRByte.Byte0
#define DDRD_BYTE1   PTD_BASE_PTR->DDRByte.Byte1
#define DDRD_BYTE2   PTD_BASE_PTR->DDRByte.Byte2
#define DDRD_BYTE3   PTD_BASE_PTR->DDRByte.Byte3

//定义PTE的8位输出输入方向  ——by 野火
#define DDRE_BYTE0   PTE_BASE_PTR->DDRByte.Byte0
#define DDRE_BYTE1   PTE_BASE_PTR->DDRByte.Byte1
#define DDRE_BYTE2   PTE_BASE_PTR->DDRByte.Byte2
#define DDRE_BYTE3   PTE_BASE_PTR->DDRByte.Byte3


//定义PTA的8位输入端口  ——by 野火
#define PTA_BYTE0_IN   PTA_BASE_PTR->PDIRByte.Byte0
#define PTA_BYTE1_IN   PTA_BASE_PTR->PDIRByte.Byte1
#define PTA_BYTE2_IN   PTA_BASE_PTR->PDIRByte.Byte2
#define PTA_BYTE3_IN   PTA_BASE_PTR->PDIRByte.Byte3

//定义PTB的8位输入端口  ——by 野火
#define PTB_BYTE0_IN   PTB_BASE_PTR->PDIRByte.Byte0
#define PTB_BYTE1_IN   PTB_BASE_PTR->PDIRByte.Byte1
#define PTB_BYTE2_IN   PTB_BASE_PTR->PDIRByte.Byte2
#define PTB_BYTE3_IN   PTB_BASE_PTR->PDIRByte.Byte3

//定义PTC的8位输入端口  ——by 野火
#define PTC_BYTE0_IN   PTC_BASE_PTR->PDIRByte.Byte0
#define PTC_BYTE1_IN   PTC_BASE_PTR->PDIRByte.Byte1
#define PTC_BYTE2_IN   PTC_BASE_PTR->PDIRByte.Byte2
#define PTC_BYTE3_IN   PTC_BASE_PTR->PDIRByte.Byte3


//定义PTD的8位输入端口  ——by 野火
#define PTD_BYTE0_IN   PTD_BASE_PTR->PDIRByte.Byte0
#define PTD_BYTE1_IN   PTD_BASE_PTR->PDIRByte.Byte1
#define PTD_BYTE2_IN   PTD_BASE_PTR->PDIRByte.Byte2
#define PTD_BYTE3_IN   PTD_BASE_PTR->PDIRByte.Byte3

//定义PTE的8位输入端口  ——by 野火
#define PTE_BYTE0_IN   PTE_BASE_PTR->PDIRByte.Byte0
#define PTE_BYTE1_IN   PTE_BASE_PTR->PDIRByte.Byte1
#define PTE_BYTE2_IN   PTE_BASE_PTR->PDIRByte.Byte2
#define PTE_BYTE3_IN   PTE_BASE_PTR->PDIRByte.Byte3


//定义PTA的16位端口  ——by 野火
#define PTA_WORD0_OUT   PTA_BASE_PTR->PDORWord.Word0
#define PTA_WORD1_OUT   PTA_BASE_PTR->PDORWord.Word1

//定义PTB的16位端口  ——by 野火
#define PTB_WORD0_OUT   PTB_BASE_PTR->PDORWord.Word0
#define PTB_WORD1_OUT   PTB_BASE_PTR->PDORWord.Word1

//定义PTC的16位端口  ——by 野火
#define PTC_WORD0_OUT   PTC_BASE_PTR->PDORWord.Word0
#define PTC_WORD1_OUT   PTC_BASE_PTR->PDORWord.Word1


//定义PTD的16位端口  ——by 野火
#define PTD_WORD0_OUT   PTD_BASE_PTR->PDORWord.Word0
#define PTD_WORD1_OUT   PTD_BASE_PTR->PDORWord.Word1


//定义PTE的16位端口  ——by 野火
#define PTE_WORD0_OUT   PTE_BASE_PTR->PDORWord.Word0
#define PTE_WORD1_OUT   PTE_BASE_PTR->PDORWord.Word1


//定义PTA的16位输出输入方向  ——by 野火
#define DDRA_WORD0   PTA_BASE_PTR->DDRWord.Word0
#define DDRA_WORD1   PTA_BASE_PTR->DDRWord.Word1


//定义PTB的16位输出输入方向  ——by 野火
#define DDRB_WORD0   PTB_BASE_PTR->DDRWord.Word0
#define DDRB_WORD1   PTB_BASE_PTR->DDRWord.Word1


//定义PTC的16位输出输入方向  ——by 野火
#define DDRC_WORD0   PTC_BASE_PTR->DDRWord.Word0
#define DDRC_WORD1   PTC_BASE_PTR->DDRWord.Word1


//定义PTD的16位输出输入方向  ——by 野火
#define DDRD_WORD0   PTD_BASE_PTR->DDRWord.Word0
#define DDRD_WORD1   PTD_BASE_PTR->DDRWord.Word1


//定义PTE的16位输出输入方向  ——by 野火
#define DDRE_WORD0   PTE_BASE_PTR->DDRWord.Word0
#define DDRE_WORD1   PTE_BASE_PTR->DDRWord.Word1


//定义PTA的16位输入端口  ——by 野火
#define PTA_WORD0_IN   PTA_BASE_PTR->PDIRWord.Word0
#define PTA_WORD1_IN   PTA_BASE_PTR->PDIRWord.Word1


//定义PTB的16位输入端口  ——by 野火
#define PTB_WORD0_IN   PTB_BASE_PTR->PDIRWord.Word0
#define PTB_WORD1_IN   PTB_BASE_PTR->PDIRWord.Word1

//定义PTC的16位输入端口  ——by 野火
#define PTC_WORD0_IN   PTC_BASE_PTR->PDIRWord.Word0
#define PTC_WORD1_IN   PTC_BASE_PTR->PDIRWord.Word1


//定义PTD的16位输入端口  ——by 野火
#define PTD_WORD0_IN   PTD_BASE_PTR->PDIRWord.Word0
#define PTD_WORD1_IN   PTD_BASE_PTR->PDIRWord.Word1


//定义PTE的16位输入端口  ——by 野火
#define PTE_WORD0_IN   PTE_BASE_PTR->PDIRWord.Word0
#define PTE_WORD1_IN   PTE_BASE_PTR->PDIRWord.Word1





typedef enum PTxn
{
    /*  PTA端口    */ //0~31
    PTA0,
    PTA1,
    PTA2,
    PTA3,
    PTA4,
    PTA5,
    PTA6,
    PTA7,
    PTA8,
    PTA9,
    PTA10,
    PTA11,
    PTA12,
    PTA13,
    PTA14,
    PTA15,
    PTA16,
    PTA17,
    PTA18,
    PTA19,
    PTA20,
    PTA21,
    PTA22,
    PTA23,
    PTA24,
    PTA25,
    PTA26,
    PTA27,
    PTA28,
    PTA29,
    PTA30,
    PTA31,

    /*  PTB端口    */   //32~63
    PTB0,
    PTB1,
    PTB2,
    PTB3,
    PTB4,
    PTB5,
    PTB6,
    PTB7,
    PTB8,
    PTB9,
    PTB10,
    PTB11,
    PTB12,
    PTB13,
    PTB14,
    PTB15,
    PTB16,
    PTB17,
    PTB18,
    PTB19,
    PTB20,
    PTB21,
    PTB22,
    PTB23,
    PTB24,
    PTB25,
    PTB26,
    PTB27,
    PTB28,
    PTB29,
    PTB30,
    PTB31,

    /*  PTC端口    */
    PTC0,
    PTC1,
    PTC2,
    PTC3,
    PTC4,
    PTC5,
    PTC6,
    PTC7,
    PTC8,
    PTC9,
    PTC10,
    PTC11,
    PTC12,
    PTC13,
    PTC14,
    PTC15,
    PTC16,
    PTC17,
    PTC18,
    PTC19,
    PTC20,
    PTC21,
    PTC22,
    PTC23,
    PTC24,
    PTC25,
    PTC26,
    PTC27,
    PTC28,
    PTC29,
    PTC30,
    PTC31,

    /*  PTD端口    */
    PTD0,
    PTD1,
    PTD2,
    PTD3,
    PTD4,
    PTD5,
    PTD6,
    PTD7,
    PTD8,
    PTD9,
    PTD10,
    PTD11,
    PTD12,
    PTD13,
    PTD14,
    PTD15,
    PTD16,
    PTD17,
    PTD18,
    PTD19,
    PTD20,
    PTD21,
    PTD22,
    PTD23,
    PTD24,
    PTD25,
    PTD26,
    PTD27,
    PTD28,
    PTD29,
    PTD30,
    PTD31,

    /*  PTE端口    */
    PTE0,
    PTE1,
    PTE2,
    PTE3,
    PTE4,
    PTE5,
    PTE6,
    PTE7,
    PTE8,
    PTE9,
    PTE10,
    PTE11,
    PTE12,
    PTE13,
    PTE14,
    PTE15,
    PTE16,
    PTE17,
    PTE18,
    PTE19,
    PTE20,
    PTE21,
    PTE22,
    PTE23,
    PTE24,
    PTE25,
    PTE26,
    PTE27,
    PTE28,
    PTE29,
    PTE30,
    PTE31,

} PTxn;


#endif
