wangdongxuking61/2015-Electronical-Competition-Code---Renesas-Cup/2015 Electronical Competition Code/src/app_mydriver/GB1616.H

#ifndef _GB1616_H
#define _GB1616_H


// ------------------  汉字字模的数据结构定义 ------------------------ //
struct  typFNT_GB16                 // 汉字字模数据结构 
{
       unsigned char  Index[3];               // 汉字内码索引	
       unsigned char   Msk[32];                        // 点阵码数据 
};

/////////////////////////////////////////////////////////////////////////
// 汉字字模表                                                          //
// 汉字库: 宋体16.dot,横向取模左高位,数据排列:从左到右从上到下         //
/////////////////////////////////////////////////////////////////////////
 struct  typFNT_GB16 codeGB_16[] =          // 数据表 
{

/*--  文字:  全  --*/
/*--  宋体12;  此字体下对应的点阵为：宽x高=16x16   --*/
"全",0x01,0x00,0x01,0x00,0x02,0x80,0x04,0x40,0x08,0x20,0x10,0x10,0x2F,0xE8,0xC1,0x06,
0x01,0x00,0x01,0x00,0x1F,0xF0,0x01,0x00,0x01,0x00,0x01,0x00,0x7F,0xFC,0x00,0x00,

/*--  文字:  动  --*/
/*--  宋体12;  此字体下对应的点阵为：宽x高=16x16   --*/
"动",0x00,0x40,0x00,0x40,0x7C,0x40,0x00,0x40,0x01,0xFC,0x00,0x44,0xFE,0x44,0x20,0x44,
0x20,0x44,0x20,0x84,0x48,0x84,0x44,0x84,0xFD,0x04,0x45,0x04,0x02,0x28,0x04,0x10,

/*--  文字:  电  --*/
/*--  宋体12;  此字体下对应的点阵为：宽x高=16x16   --*/
"电",0x01,0x00,0x01,0x00,0x01,0x00,0x3F,0xF8,0x21,0x08,0x21,0x08,0x3F,0xF8,0x21,0x08,
0x21,0x08,0x21,0x08,0x3F,0xF8,0x21,0x08,0x01,0x02,0x01,0x02,0x00,0xFE,0x00,0x00,

/*--  文字:  子  --*/
/*--  宋体12;  此字体下对应的点阵为：宽x高=16x16   --*/
"子",0x00,0x00,0x3F,0xF0,0x00,0x20,0x00,0x40,0x00,0x80,0x01,0x00,0x01,0x00,0x01,0x04,
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

/*--  文字:  持  --*/
/*--  宋体12;  此字体下对应的点阵为：宽x高=16x16   --*/
"持",0x10,0x40,0x10,0x40,0x13,0xFC,0xFC,0x40,0x10,0x40,0x17,0xFE,0x14,0x10,0x18,0x10,
0x37,0xFE,0xD0,0x10,0x11,0x10,0x10,0xD0,0x10,0x90,0x10,0x10,0x50,0x50,0x20,0x20,

/*--  文字:  论  --*/
/*--  宋体12;  此字体下对应的点阵为：宽x高=16x16   --*/
"论",0x40,0x40,0x20,0x40,0x30,0xA0,0x20,0x90,0x01,0x08,0x02,0x06,0xE5,0x04,0x21,0x10,
0x21,0x38,0x21,0xC0,0x21,0x00,0x25,0x00,0x29,0x04,0x31,0x04,0x20,0xFC,0x00,0x00,

/*--  文字:  坛  --*/
/*--  宋体12;  此字体下对应的点阵为：宽x高=16x16   --*/
"坛",0x00,0x00,0x11,0xFC,0x10,0x00,0x10,0x00,0x10,0x00,0xFC,0x00,0x13,0xFE,0x10,0x40,
0x10,0x60,0x10,0x80,0x1C,0x88,0x31,0x04,0xC2,0x7E,0x07,0xC6,0x02,0x04,0x00,0x00,




};
#endif
