wangdongxuking61/2015-Electronical-Competition-Code---Renesas-Cup/2015 Electronical Competition Code/src/app/isr.h

#ifndef __ISR_H
#define __ISR_H 1

#include  "include.h"

/*                          重新定义中断向量表
 *  先取消默认的中断向量元素宏定义       #undef  VECTOR_xxx
 *  在重新定义到自己编写的中断函数       #define VECTOR_xxx    xxx_IRQHandler
 *  例如：
 *       #undef  VECTOR_003
 *       #define VECTOR_003    HardFault_Handler    重新定义硬件上访中断服务函数
 */
#undef  VECTOR_014
#undef  VECTOR_015
#if     USOC_EN > 0u    //如果定义了用ucos系统  用ucos的滴答定时器中断服务函数
#define VECTOR_014    OS_CPU_PendSVHandler
#define VECTOR_015    OS_CPU_SysTickHandler
#else
#define VECTOR_014    PendSV_Handler
#define VECTOR_015    SysTick_Handler   //滴答定时器  OS用得到
#endif

#undef  VECTOR_003
#define VECTOR_003    HardFault_Handler   //发生硬件上访 （就是程序跑飞了）     推荐调试程序时，用个LED显示来指示程序跑飞了

#undef  VECTOR_064                        //要先取消了，因为在vectors.h里默认是定义为 default_isr  
#define VECTOR_064    USART0_IRQHandler   //重新定义63号中断的ISR：UART1：Single interrupt vector for UART status sources

#undef  VECTOR_078
#define VECTOR_078    FTM0_IRQHandler     //FTM0输入捕捉中断 

#undef  VECTOR_079
#define VECTOR_079    FTM1_IRQHandler     //FTM0输入捕捉中断

#undef  VECTOR_084
#define VECTOR_084    PIT0_IRQHandler     //重新定义84号中断为PIT0_IRQHandler中断

#undef  VECTOR_104
#define VECTOR_104    PORTB_IRQHandler    //重新定义104号中断为PORTB_IRQHandler中断 

#undef  VECTOR_106
#define VECTOR_106    VSYNC_IRQ           //重新定义106号中断为VSYNC_IRQ中断 

#undef  VECTOR_016
#define VECTOR_016    DMA0_IRQHandler
/********************************************************************************/


extern void PendSV_Handler(void);         //可悬起的系统调用中断服务函数
extern void HardFault_Handler(void);      //发生硬件上访（程序跑飞）
extern void SysTick_Handler(void);        //滴答时钟(os 用到)
extern void USART0_IRQHandler();          //串口1 中断接收函数
extern void PIT0_IRQHandler();            //PIT0 定时中断服务函数
extern void PORTB_IRQHandler();           //PORTB中断服务函数
extern void VSYNC_IRQ();                  //PORTD中断服务函数
extern void FTM0_IRQHandler();            //FTM0输入捕捉中断
extern void FTM1_IRQHandler();            //FTM0输入捕捉中断
extern void DMA0_IRQHandler();


#endif  //__ISR_H

/* End of "isr.h" */
