wangdongxuking61/2015-Electronical-Competition-Code---Renesas-Cup/2015 Electronical Competition Code/src/app_mydriver/IMAQ.c

#include "IMAQ.h"

/******************** (C) COPYRIGHT 2011 野火嵌入式开发工作室 ********************
 * 文件名       ：IMAQ.c
 * 描述         ：要采集的图像数据行数
 * 实验平台     ：凌立印象开发板
 * 库版本       ：基于野火库
 * 嵌入系统     ：
 * 作者         ：xuxu
**********************************************************************************/


const uint16 Wanted_HREF_Debug[]=
{
    0,  1,  2,  3,  4,  6,  7,  8,  9, 10,
   12, 13, 14, 15, 16, 18, 19, 20, 21, 22,
   24, 25, 26, 27, 28, 30, 31, 32, 33, 34,
   36, 37, 38, 39, 40, 42, 43, 44, 45, 46,
   48, 49, 50, 51, 52, 54, 55, 56, 57, 58,
   60, 61, 62, 63, 64, 66, 67, 68, 69, 70,
   72, 73, 74, 75, 76, 78, 79, 80, 81, 82,
   84, 85, 86, 87, 88, 90, 91, 92, 93, 94,
   96, 97, 98, 99,100,102,103,104,105,106,
  108,109,110,111,112,114,115,116,117,118,//100行
  120,121,122,123,124,126,127,128,129,130,
  132,133,134,135,136,138,139,140,141,142,
  144,145,146,147,148,150,151,152,153,154,
  156,157,158,159,160,162,163,164,165,166,
  168,169,170,171,172,174,175,176,177,178,//150
  180,181,182,183,184,186,187,188,189,190,
  192,193,194,195,196,198,199,200,201,202,
  203,204,205,206,207,208,210,211,212,213,
  214,215,216,217,218,219,220,222,223,224,
  225,226,227,228,229,230,231,232,234,235,//200行
  236,237
};//200+2个行
const uint16 Wanted_HREF_Run[]=
{
    0,  4,  8, 10, 12, 16, 18, 22, 24, 28,
   32, 34, 38, 40, 42, 44, 48, 50, 54, 56,
   58, 60, 62, 64, 66, 68, 70, 72, 74, 76,
   78, 80, 82, 84, 86, 88, 90, 92, 94, 96,
   98,100,102,104,106,108,110,112,114,116,
  118,120,122,124,126,128,130,132,134,136,
  138,140,142,144,146,148,150,152,154,156,
  158,160,162,164,166,168,170,172,174,176,
  178,180,182,184,186,188,190,192,194,196,
  198,200,202,204,206,208,210,212,214,216,
  218,220//100行
};//102+2个行

uint16 const *Wanted_HREF;
vuint16 HREF_counter = 0;
vuint16 Valid_HREF_counter = 0;
vuint16  Max_HREF;
