wangdongxuking61/2015-Electronical-Competition-Code---Renesas-Cup/2015 Electronical Competition Code/src/app_mydriver/IMAQ.h

#ifndef __IMAQ_H__
#define __IMAQ_H__

#include "common.h"

extern const uint16 Wanted_HREF_Debug[];
extern const uint16 Wanted_HREF_Run[];
extern uint16 const *Wanted_HREF;

extern vuint16 HREF_counter;
extern vuint16 Valid_HREF_counter; 
extern vuint16 Max_HREF; 


#endif 
