wangdongxuking61/2015-Electronical-Competition-Code---Renesas-Cup/2015 Electronical Competition Code/src/app_mydriver/mytype.h

#ifndef _MYTYPE_H_
#define _MYTYPE_H_
 
#define UINT8   unsigned char
#define UINT16  unsigned short int
#define UINT32  unsigned int 

#define INT8    char   
#define INT16   short int 
#define INT32   int 

#endif
