wangdongxuking61/2015-Electronical-Competition-Code---Renesas-Cup/2015 Electronical Competition Code/src/common/io.c

/*
 * File:		io.c
 * Purpose:		Serial Input/Output routines
 *
 * Notes:       TERMINAL_PORT defined in <board>.h
 */

#include "common.h"
#include "uart.h"

/********************************************************************/
char
in_char (void)
{
    return uart_getchar(FIRE_PORT);
}
/********************************************************************/
void
out_char (char ch)
{
    uart_putchar(FIRE_PORT, ch);
}
/********************************************************************/
int
char_present (void)
{
    return uart_query(FIRE_PORT);
}
/********************************************************************/
