wangdongxuking61/2015-Electronical-Competition-Code---Renesas-Cup/2015 Electronical Competition Code/src/common/queue.c

/*
 * File:    queue.c
 * Purpose: Implement a first in, first out linked list
 *
 * Notes:
 */

#include "common.h"
#include "queue.h"

/********************************************************************/
/*
 * Initialize the specified queue to an empty state
 *
 * Parameters:
 *  q   Pointer to queue structure
 */
void
queue_init(QUEUE *q)
{
    q->head = NULL;
}
/********************************************************************/
/*
 * Check for an empty queue
 *
 * Parameters:
 *  q       Pointer to queue structure
 *
 * Return Value:
 *  1 if Queue is empty
 *  0 otherwise
 */
int
queue_isempty(QUEUE *q)
{
    return (q->head == NULL);
}
/********************************************************************/
/*
 * Add an item to the end of the queue
 *
 * Parameters:
 *  q       Pointer to queue structure
 *  node    New node to add to the queue
 */
void
queue_add(QUEUE *q, QNODE *node)
{
    if (queue_isempty(q))
    {
        q->head = q->tail = node;
    }
    else
    {
        q->tail->next = node;
        q->tail = node;
    }

    node->next = NULL;
}

/********************************************************************/
/*
 * Remove and return first (oldest) entry from the specified queue
 *
 * Parameters:
 *  q       Pointer to queue structure
 *
 * Return Value:
 *  Node at head of queue - NULL if queue is empty
 */
QNODE*
queue_remove(QUEUE *q)
{
    QNODE *oldest;

    if (queue_isempty(q))
        return NULL;

    oldest = q->head;
    q->head = oldest->next;
    return oldest;
}
/********************************************************************/
/*
 * Peek into the queue and return pointer to first (oldest) entry.
 * The queue is not modified
 *
 * Parameters:
 *  q       Pointer to queue structure
 *
 * Return Value:
 *  Node at head of queue - NULL if queue is empty
 */
QNODE*
queue_peek(QUEUE *q)
{
    return q->head;
}
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
